Finomnis/NixieClock/Firmware/NixieClock/src/Settings.h

#pragma once

#include <Arduino.h>

struct Settings_t
{
    bool COLON_BLINK_EVERY_SECOND = false;
    bool COLON_BLINK_ON_SYNC = false;
    bool DISPLAY_RENDER_TO_CONSOLE = true;
    bool RESET_RTC_ON_STARTUP = false;
    unsigned long TIME_UNTIL_DCF_ANIMATION_SHOWS_AGAIN = 4L * 60L * 60L * 1000L; // Four Hours (from time zone change to morning)
    bool SHOW_DCF_ANIMATION_AGAIN_AFTER_TIMEOUT = false;

    // Dimming
    bool DISPLAY_DIM_AT_NIGHT = true;
    uint8_t DISPLAY_DIM_BRIGHTNESS = 20;
    uint16_t DISPLAY_DIM_START = 22 * 60;
    uint16_t DISPLAY_DIM_END = 7 * 60;
    unsigned long DISPLAY_DIM_ANIMATION_DURATION = 40000;

    // Timezone
    int TIMEZONE_0 = 1;
    int TIMEZONE_1 = 2;
};

extern const Settings_t Settings;
